hanzamzamy/arb-fpro/Dokumentasi/1.jpg

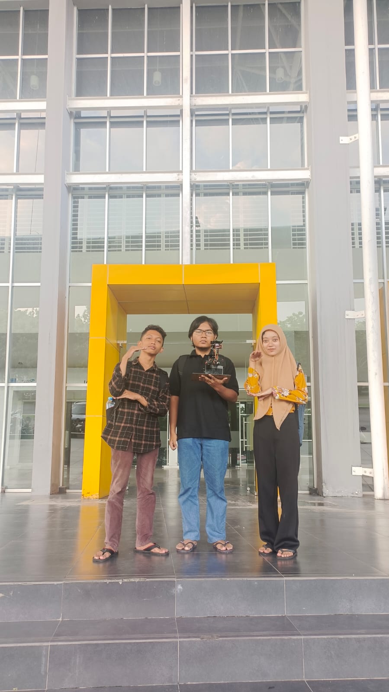
Dokumentasi/1.jpg
