hanzamzamy/arb-fpro/Dokumentasi/2.jpg

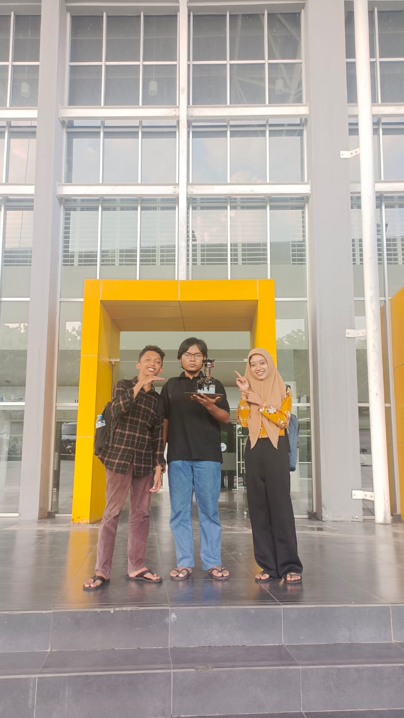
Dokumentasi/2.jpg
