hanzamzamy/arb-fpro/Dokumentasi/Barang e.jpg

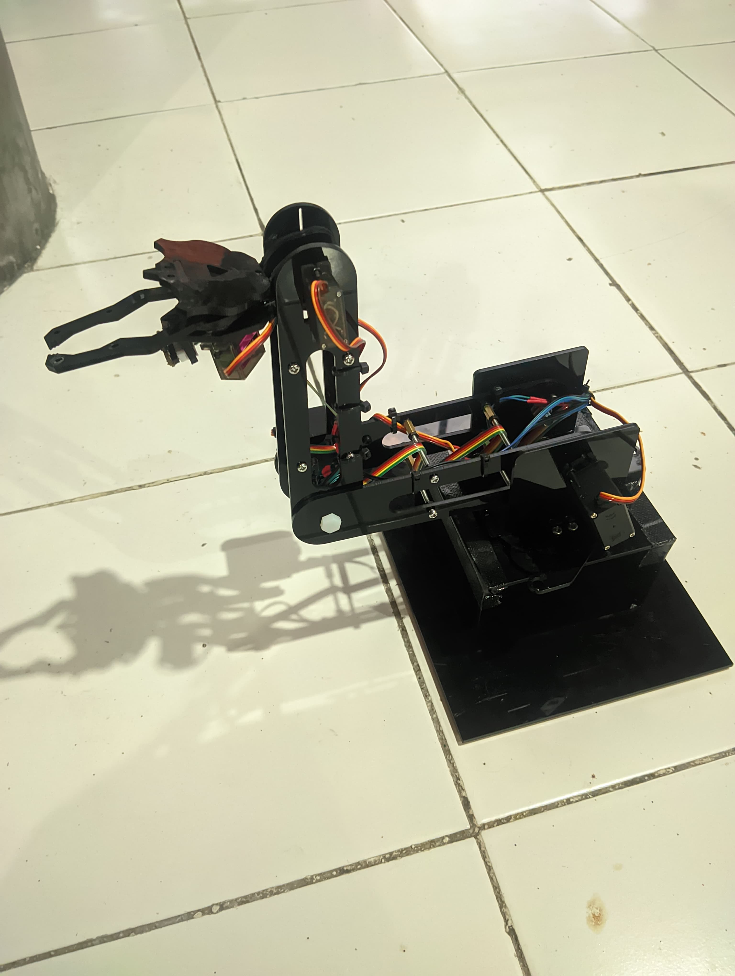
Dokumentasi/Barang e.jpg
