hanzamzamy/arb-fpro/Electrical/FP_Abinara/Controller_Render Bottom.png

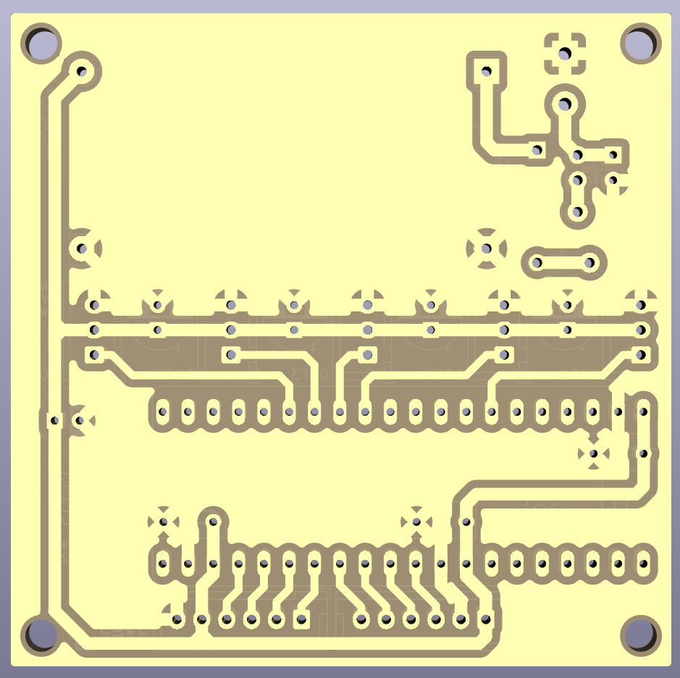
Electrical/FP_Abinara/Controller_Render Bottom.png
