hanzamzamy/arb-fpro/Electrical/FP_Abinara/Controller_Render Top.png

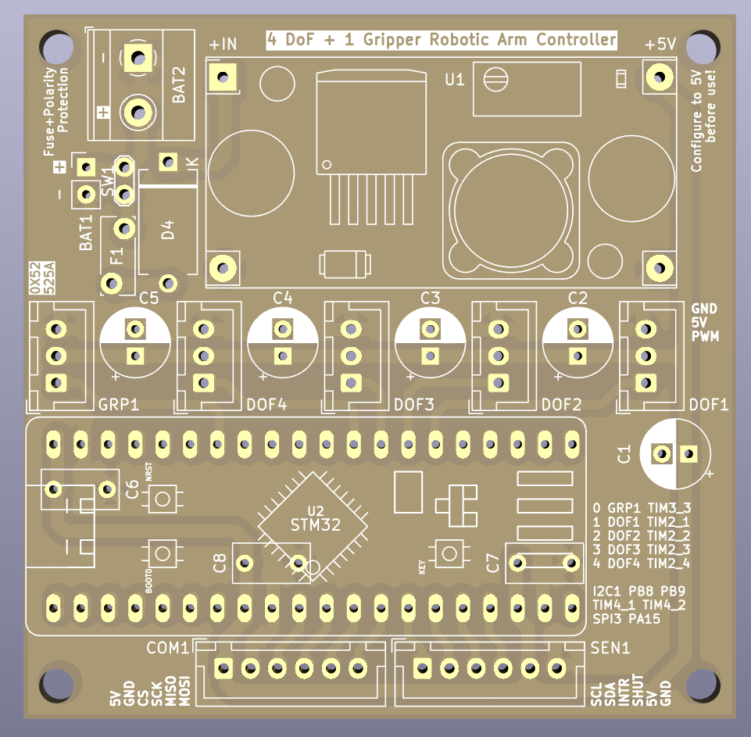
Electrical/FP_Abinara/Controller_Render Top.png
