hanzamzamy/arb-fpro/Mechanical/Macrobot_Silvia Nur Aziza_Mechanical/1b70d2714a9770270d7ed8d73e5aa972.jpg

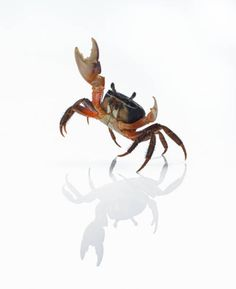
Mechanical/Macrobot_Silvia Nur Aziza_Mechanical/1b70d2714a9770270d7ed8d73e5aa972.jpg
