hanzamzamy/arb-fpro/Mechanical/Macrobot_Silvia Nur Aziza_Mechanical/1f14c011dfd35143ff6038cf6c039e9c.jpg

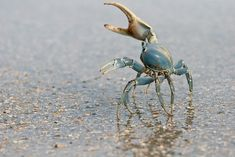
Mechanical/Macrobot_Silvia Nur Aziza_Mechanical/1f14c011dfd35143ff6038cf6c039e9c.jpg
