hanzamzamy/arb-fpro/Mechanical/Macrobot_Silvia Nur Aziza_Mechanical/5ebacc5fd523165728d35504ef82c865.jpg

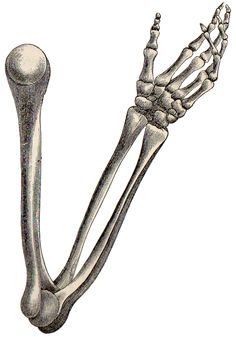
Mechanical/Macrobot_Silvia Nur Aziza_Mechanical/5ebacc5fd523165728d35504ef82c865.jpg
