hanzamzamy/arb-fpro/Mechanical/Macrobot_Silvia Nur Aziza_Mechanical/6f040f222747fe39410e0ac93c5bb1eb.jpg

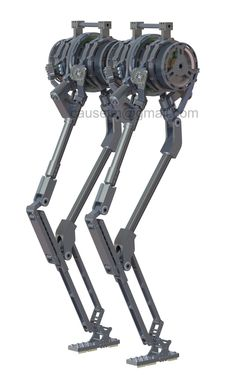
Mechanical/Macrobot_Silvia Nur Aziza_Mechanical/6f040f222747fe39410e0ac93c5bb1eb.jpg
