hanzamzamy/arb-fpro/Mechanical/Macrobot_Silvia Nur Aziza_Mechanical/7bddb617da2399516741761e50cced2f.jpg

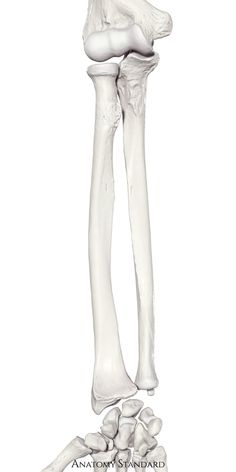
Mechanical/Macrobot_Silvia Nur Aziza_Mechanical/7bddb617da2399516741761e50cced2f.jpg
