hanzamzamy/arb-fpro/Mechanical/Macrobot_Silvia Nur Aziza_Mechanical/9b21c861dd7363406e4008cd5ddb0c76.jpg

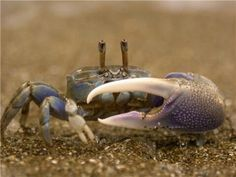
Mechanical/Macrobot_Silvia Nur Aziza_Mechanical/9b21c861dd7363406e4008cd5ddb0c76.jpg
