hanzamzamy/arb-fpro/Mechanical/Macrobot_Silvia Nur Aziza_Mechanical/22eb1ead862de790698cb6ff54a92b3c.jpg

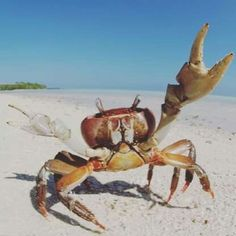
Mechanical/Macrobot_Silvia Nur Aziza_Mechanical/22eb1ead862de790698cb6ff54a92b3c.jpg
