hanzamzamy/arb-fpro/Mechanical/Macrobot_Silvia Nur Aziza_Mechanical/24a283ecc0165925ef94e39cae853259.jpg

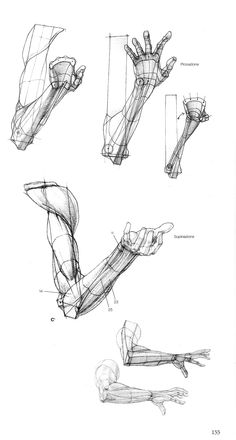
Mechanical/Macrobot_Silvia Nur Aziza_Mechanical/24a283ecc0165925ef94e39cae853259.jpg
