hanzamzamy/arb-fpro/Mechanical/Macrobot_Silvia Nur Aziza_Mechanical/52b4f24d89aa3ba14f1d6c219212160f.jpg

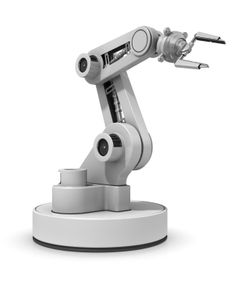
Mechanical/Macrobot_Silvia Nur Aziza_Mechanical/52b4f24d89aa3ba14f1d6c219212160f.jpg
