hanzamzamy/arb-fpro/Mechanical/Macrobot_Silvia Nur Aziza_Mechanical/71ebfb8fe3e344c98b983a9f49a2de56.jpg

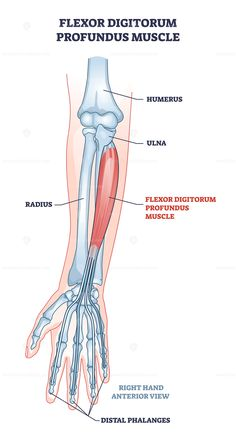
Mechanical/Macrobot_Silvia Nur Aziza_Mechanical/71ebfb8fe3e344c98b983a9f49a2de56.jpg
