hanzamzamy/arb-fpro/Mechanical/Macrobot_Silvia Nur Aziza_Mechanical/74ea5ec94e9108678c05d65d293ccad4.jpg

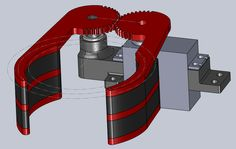
Mechanical/Macrobot_Silvia Nur Aziza_Mechanical/74ea5ec94e9108678c05d65d293ccad4.jpg
