hanzamzamy/arb-fpro/Mechanical/Macrobot_Silvia Nur Aziza_Mechanical/83fee2618bc4fb25e195a0beeff81b47.jpg

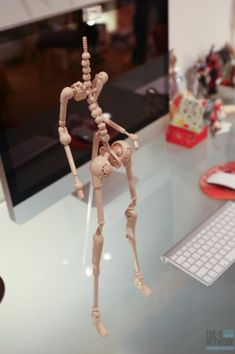
Mechanical/Macrobot_Silvia Nur Aziza_Mechanical/83fee2618bc4fb25e195a0beeff81b47.jpg
