hanzamzamy/arb-fpro/Mechanical/Macrobot_Silvia Nur Aziza_Mechanical/400e2da95c83461e85157f70f1b9e926.jpg

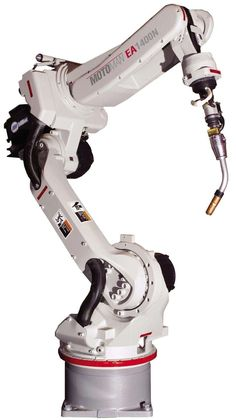
Mechanical/Macrobot_Silvia Nur Aziza_Mechanical/400e2da95c83461e85157f70f1b9e926.jpg
