hanzamzamy/arb-fpro/Mechanical/Macrobot_Silvia Nur Aziza_Mechanical/895d9e59c8b177fc4fbb9f1e9df40633.jpg

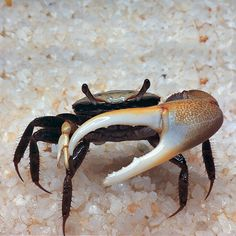
Mechanical/Macrobot_Silvia Nur Aziza_Mechanical/895d9e59c8b177fc4fbb9f1e9df40633.jpg
