hanzamzamy/arb-fpro/Mechanical/Macrobot_Silvia Nur Aziza_Mechanical/4187bd70cf4623def9ee9aae4583c98c.jpg

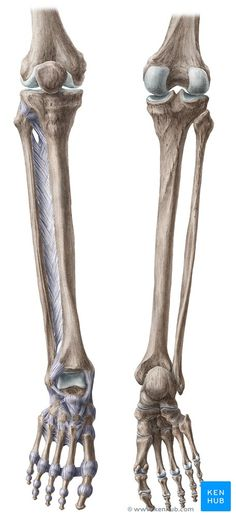
Mechanical/Macrobot_Silvia Nur Aziza_Mechanical/4187bd70cf4623def9ee9aae4583c98c.jpg
