hanzamzamy/arb-fpro/Mechanical/Macrobot_Silvia Nur Aziza_Mechanical/19350de375ecb00b500f2bd80deb1692.jpg

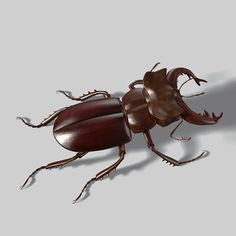
Mechanical/Macrobot_Silvia Nur Aziza_Mechanical/19350de375ecb00b500f2bd80deb1692.jpg
