hanzamzamy/arb-fpro/Mechanical/Macrobot_Silvia Nur Aziza_Mechanical/71604eb40ae7a4ac1df7c45119ac012c.jpg

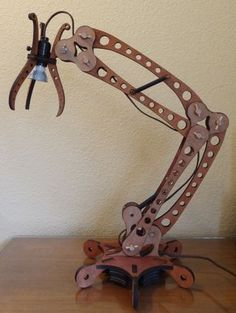
Mechanical/Macrobot_Silvia Nur Aziza_Mechanical/71604eb40ae7a4ac1df7c45119ac012c.jpg
