hanzamzamy/arb-fpro/Mechanical/Macrobot_Silvia Nur Aziza_Mechanical/97079ea19a3d9b3a081851db0ce27ebf.jpg

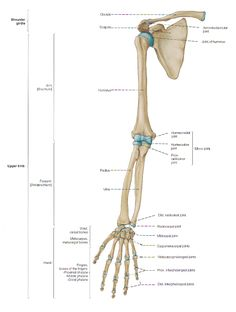
Mechanical/Macrobot_Silvia Nur Aziza_Mechanical/97079ea19a3d9b3a081851db0ce27ebf.jpg
