hanzamzamy/arb-fpro/Mechanical/Macrobot_Silvia Nur Aziza_Mechanical/848779f3e6584e807d604cdb2f7c47b8.jpg

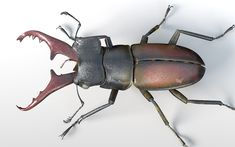
Mechanical/Macrobot_Silvia Nur Aziza_Mechanical/848779f3e6584e807d604cdb2f7c47b8.jpg
