hanzamzamy/arb-fpro/Mechanical/Macrobot_Silvia Nur Aziza_Mechanical/c9f90fcedc622ee27020b8a11ae0bc79.jpg

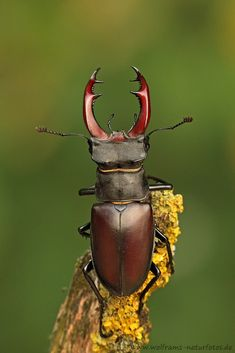
Mechanical/Macrobot_Silvia Nur Aziza_Mechanical/c9f90fcedc622ee27020b8a11ae0bc79.jpg
