hanzamzamy/arb-fpro/Mechanical/Macrobot_Silvia Nur Aziza_Mechanical/c50b781b7837ca079c64433cbba6b4cd.jpg

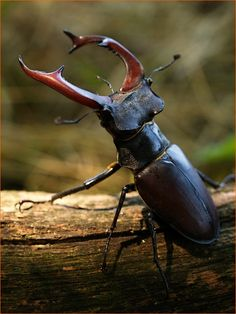
Mechanical/Macrobot_Silvia Nur Aziza_Mechanical/c50b781b7837ca079c64433cbba6b4cd.jpg
