hanzamzamy/arb-fpro/Mechanical/Macrobot_Silvia Nur Aziza_Mechanical/cb312d82ace88d422fab98ad79ffac79.jpg

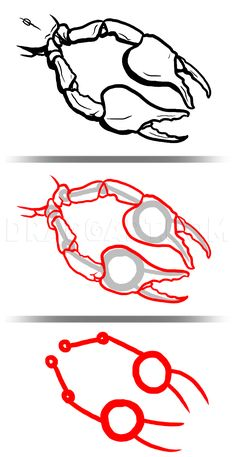
Mechanical/Macrobot_Silvia Nur Aziza_Mechanical/cb312d82ace88d422fab98ad79ffac79.jpg
