hanzamzamy/arb-fpro/Mechanical/Macrobot_Silvia Nur Aziza_Mechanical/debb197d7bb12a75175ac4dd222c4765.jpg

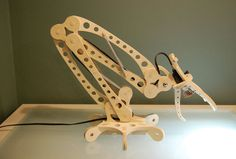
Mechanical/Macrobot_Silvia Nur Aziza_Mechanical/debb197d7bb12a75175ac4dd222c4765.jpg
