hanzamzamy/arb-fpro/Mechanical/Macrobot_Silvia Nur Aziza_Mechanical/e524af7c66d48fa53c7d827c05bd7dcf.jpg

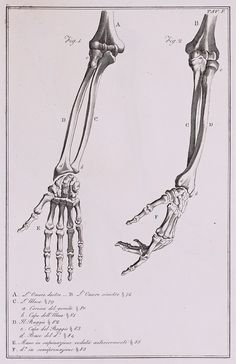
Mechanical/Macrobot_Silvia Nur Aziza_Mechanical/e524af7c66d48fa53c7d827c05bd7dcf.jpg
