hanzamzamy/arb-fpro/Mechanical/Macrobot_Silvia Nur Aziza_Mechanical/WhatsApp Image 2024-02-11 at 00.09.53 (1).jpeg

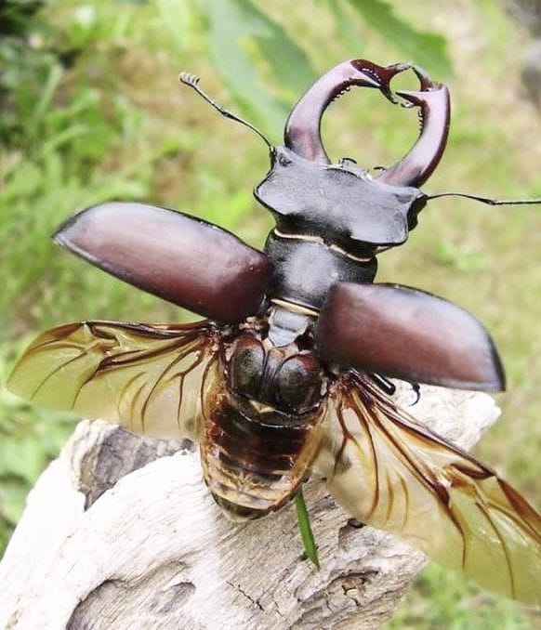
Mechanical/Macrobot_Silvia Nur Aziza_Mechanical/WhatsApp Image 2024-02-11 at 00.09.53 (1).jpeg
