hanzamzamy/arb-fpro/Mechanical/Macrobot_Silvia Nur Aziza_Mechanical/WhatsApp Image 2024-02-11 at 09.15.11 (1).jpeg

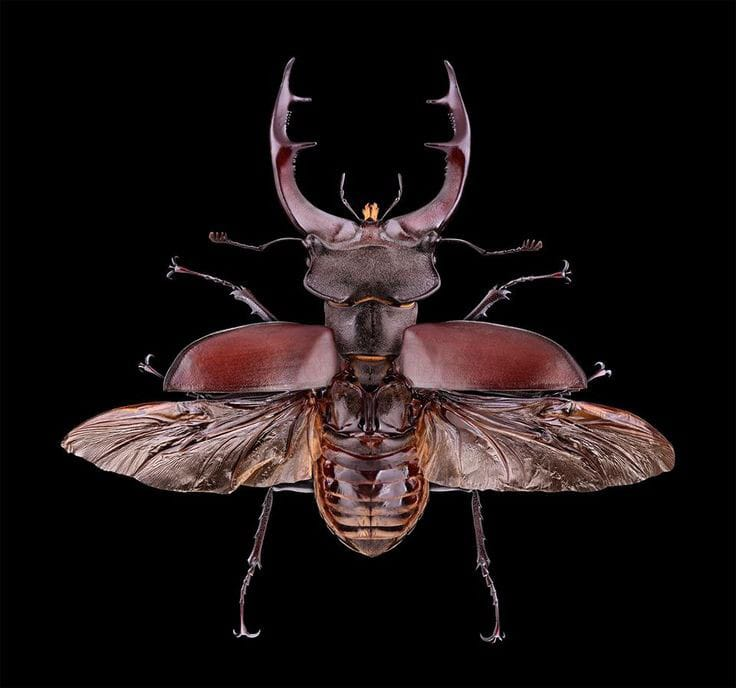
Mechanical/Macrobot_Silvia Nur Aziza_Mechanical/WhatsApp Image 2024-02-11 at 09.15.11 (1).jpeg
