hanzamzamy/arb-fpro/Programming/easeinout.png

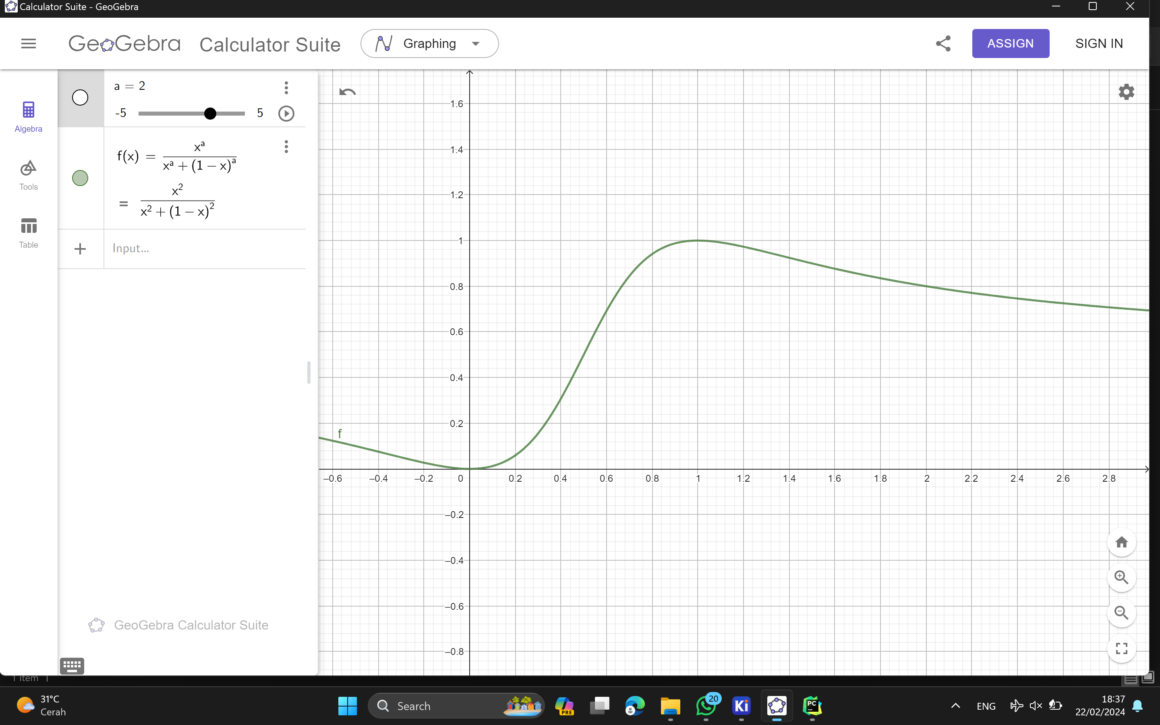
Programming/easeinout.png
