hanzamzamy/arb-fpro/Programming/urdfmodel.png

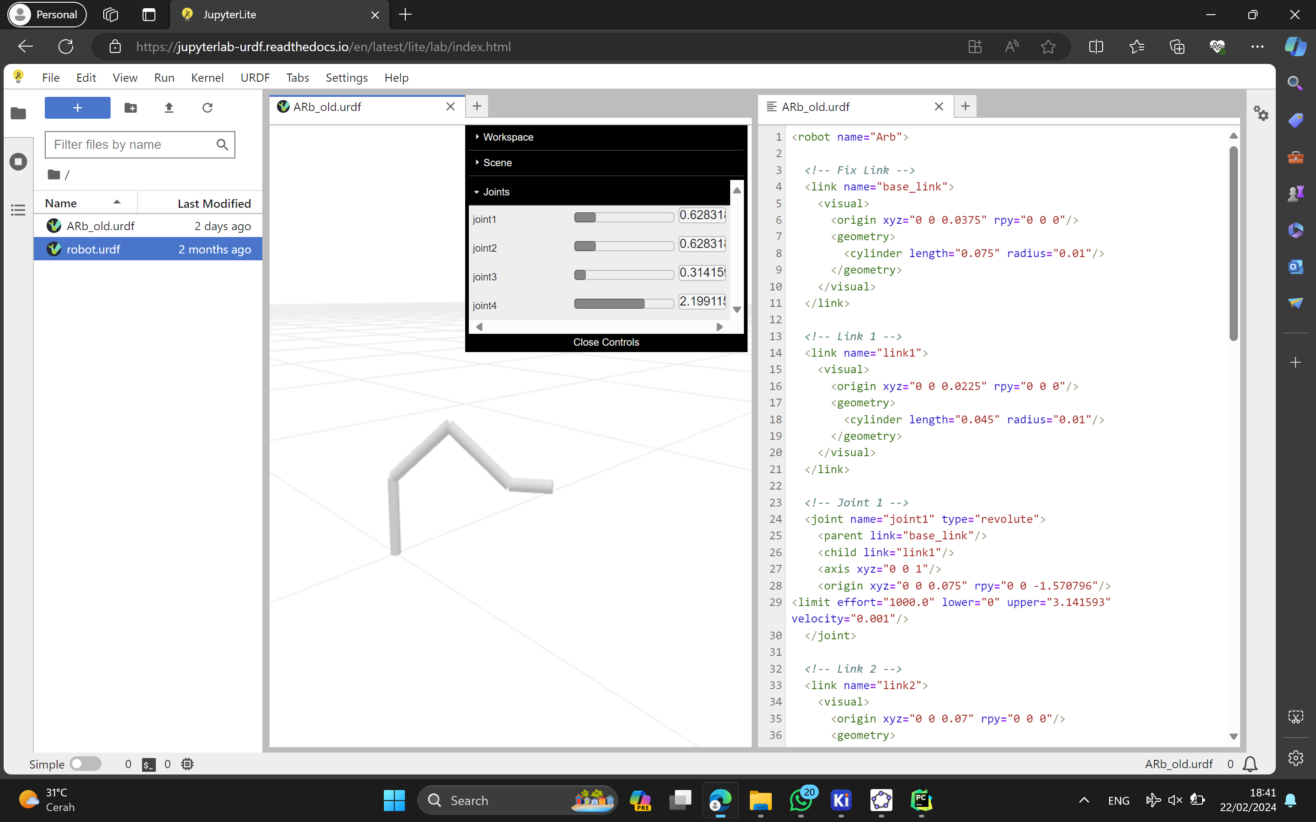
Programming/urdfmodel.png
