hanzamzamy/arb-fpro/Mechanical/Macrobot_Silvia Nur Aziza_Mechanical/mg996-servo-motor-180-1.snapshot.1/Servo MG995 180/Servo MG995.SLDPRT

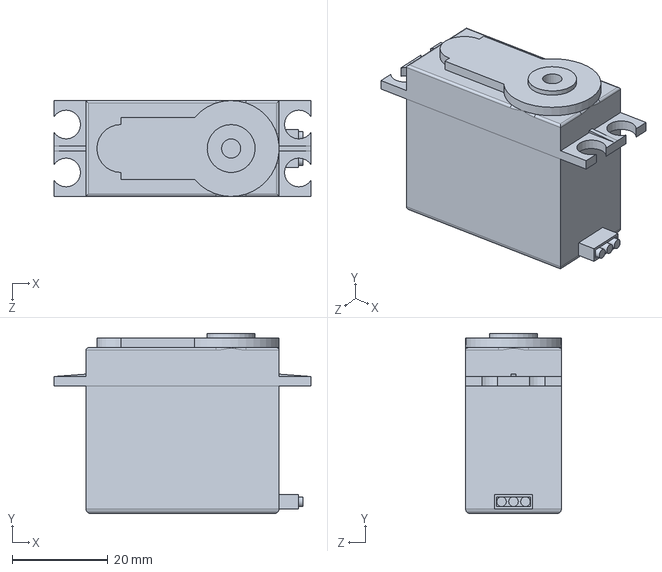
[picture p57: CAD file, 2024-02-22]
Mechanical/Macrobot_Silvia Nur Aziza_Mechanical/mg996-servo-motor-180-1.snapshot.1/Servo MG995 180/Servo MG995.SLDPRT
53.6 x 37.6 x 20.0 mm
