hanzamzamy/arb-fpro/Mechanical/Macrobot_Silvia Nur Aziza_Mechanical/refisni/db 2 - Copy.SLDPRT

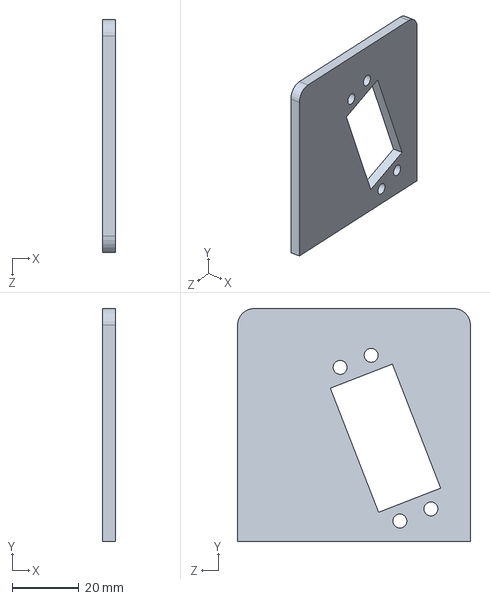
[picture p58: CAD file, 2024-02-22]
Mechanical/Macrobot_Silvia Nur Aziza_Mechanical/refisni/db 2 - Copy.SLDPRT
4.00 x 70.0 x 70.0 mm
