hanzamzamy/arb-fpro/Mechanical/Macrobot_Silvia Nur Aziza_Mechanical/kiri untuk perhitungan sketsa.SLDPRT

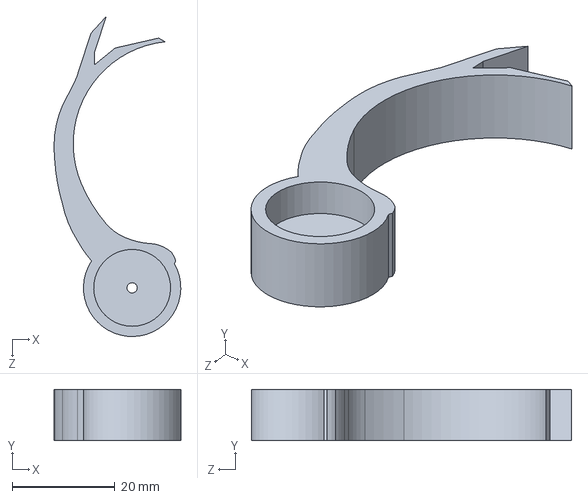
[picture p59: CAD file, 2024-02-22]
Mechanical/Macrobot_Silvia Nur Aziza_Mechanical/kiri untuk perhitungan sketsa.SLDPRT
24.7 x 10.0 x 62.4 mm
