hanzamzamy/arb-fpro/Mechanical/Macrobot_Silvia Nur Aziza_Mechanical/FP23_Object.SLDPRT

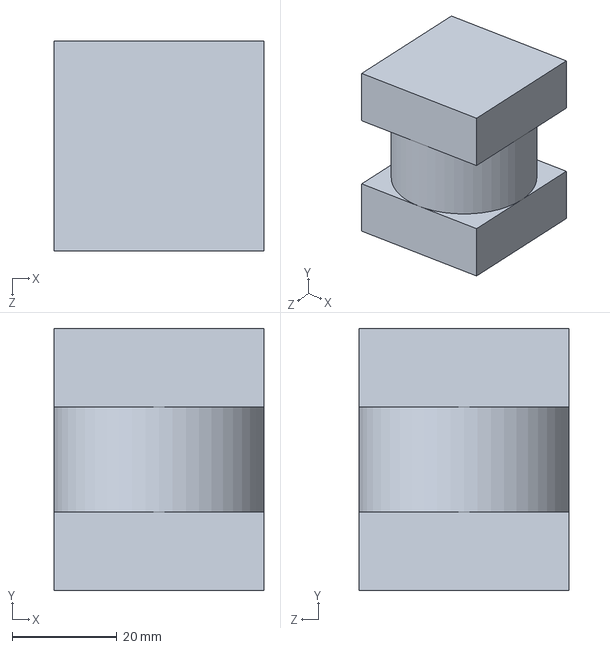
[picture p60: CAD file, 2024-02-22]
Mechanical/Macrobot_Silvia Nur Aziza_Mechanical/FP23_Object.SLDPRT
40.0 x 50.0 x 40.0 mm
