hanzamzamy/arb-fpro/Mechanical/Macrobot_Silvia Nur Aziza_Mechanical/refisni/revisi base.SLDPRT

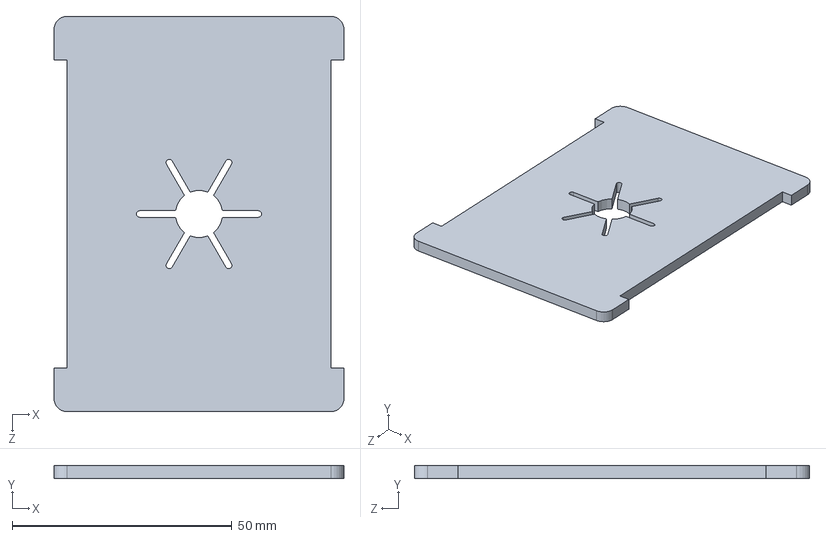
[picture p61: CAD file, 2024-02-22]
Mechanical/Macrobot_Silvia Nur Aziza_Mechanical/refisni/revisi base.SLDPRT
66.0 x 3.00 x 90.0 mm
