hanzamzamy/arb-fpro/Mechanical/Macrobot_Silvia Nur Aziza_Mechanical/refisni/bawah - Copy.SLDPRT

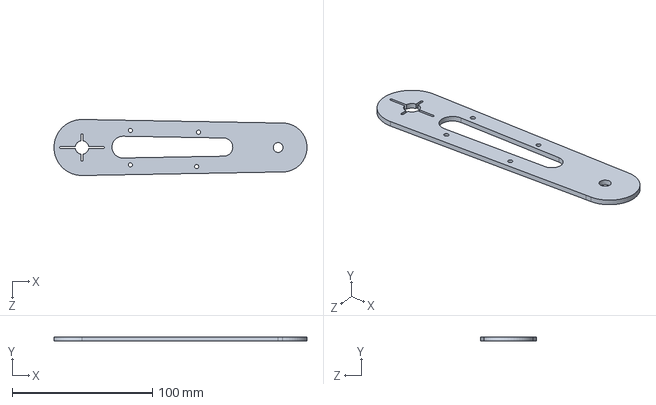
[picture p62: CAD file, 2024-02-22]
Mechanical/Macrobot_Silvia Nur Aziza_Mechanical/refisni/bawah - Copy.SLDPRT
180.6 x 3.00 x 40.0 mm
