hanzamzamy/arb-fpro/Mechanical/Macrobot_Silvia Nur Aziza_Mechanical/monting.SLDPRT

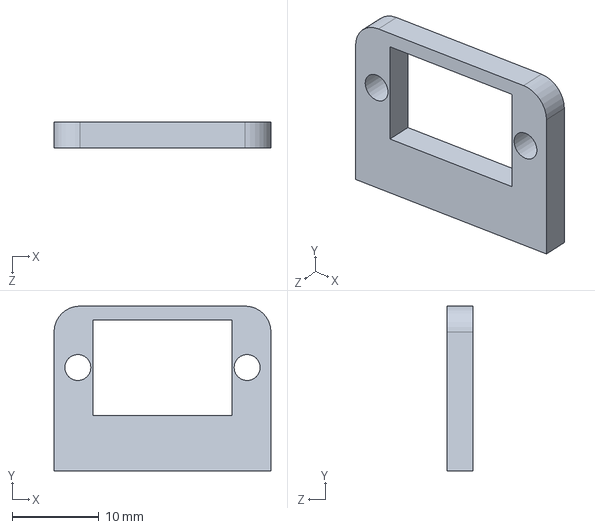
[picture p63: CAD file, 2024-02-22]
Mechanical/Macrobot_Silvia Nur Aziza_Mechanical/monting.SLDPRT
25.0 x 19.0 x 3.00 mm
