hanzamzamy/arb-fpro/Mechanical/Macrobot_Silvia Nur Aziza_Mechanical/0atas kiri pjg.SLDPRT

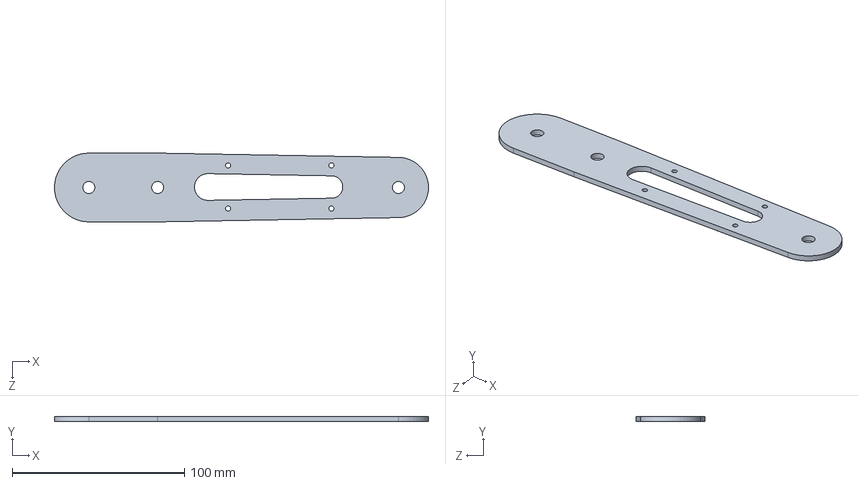
[picture p64: CAD file, 2024-02-22]
Mechanical/Macrobot_Silvia Nur Aziza_Mechanical/0atas kiri pjg.SLDPRT
217.4 x 3.00 x 40.0 mm
