hanzamzamy/arb-fpro/Mechanical/Macrobot_Silvia Nur Aziza_Mechanical/kanan fiks.SLDPRT

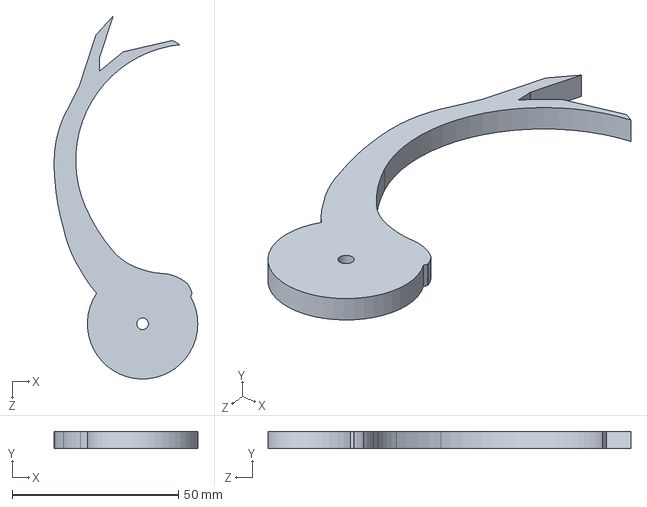
[picture p65: CAD file, 2024-02-22]
Mechanical/Macrobot_Silvia Nur Aziza_Mechanical/kanan fiks.SLDPRT
43.2 x 5.25 x 109.3 mm
