hanzamzamy/arb-fpro/Mechanical/Macrobot_Silvia Nur Aziza_Mechanical/tatakan griper bawah - Copy.SLDPRT

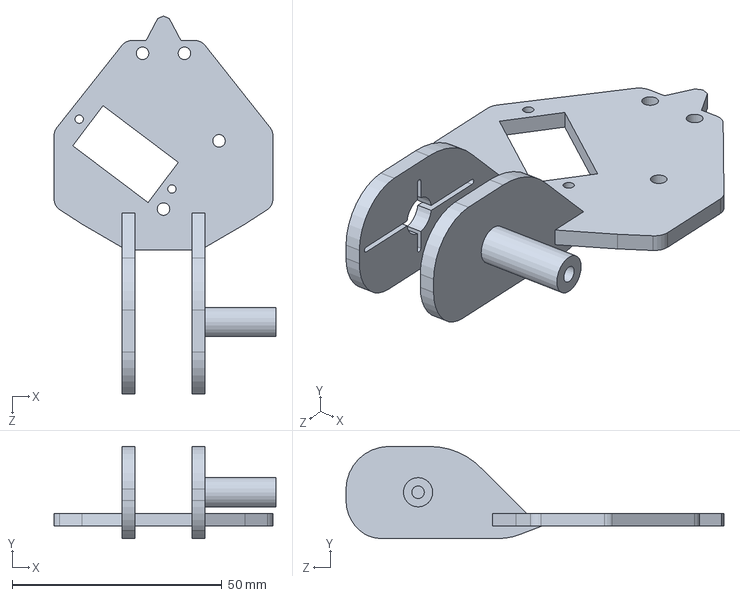
[picture p66: CAD file, 2024-02-22]
Mechanical/Macrobot_Silvia Nur Aziza_Mechanical/tatakan griper bawah - Copy.SLDPRT
53.0 x 22.0 x 90.2 mm
