hanzamzamy/arb-fpro/Mechanical/Macrobot_Silvia Nur Aziza_Mechanical/bassseeesss.SLDPRT

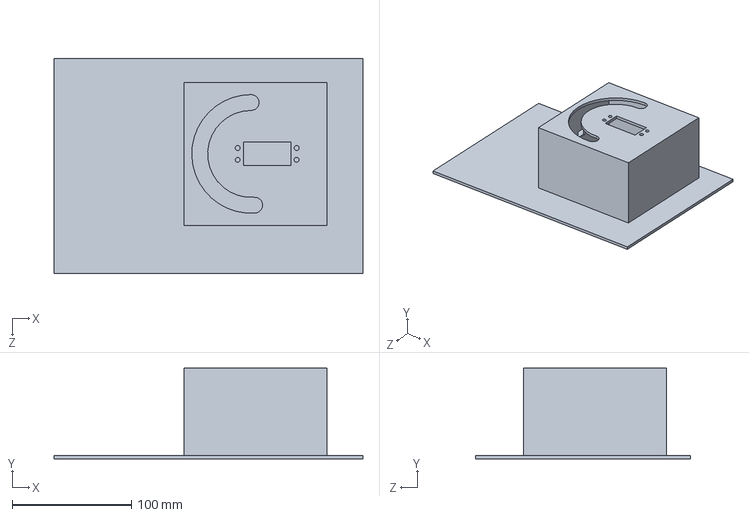
[picture p67: CAD file, 2024-02-22]
Mechanical/Macrobot_Silvia Nur Aziza_Mechanical/bassseeesss.SLDPRT
259.0 x 76.0 x 180.3 mm
