hanzamzamy/arb-fpro/Mechanical/Macrobot_Silvia Nur Aziza_Mechanical/kiri baguss.SLDPRT

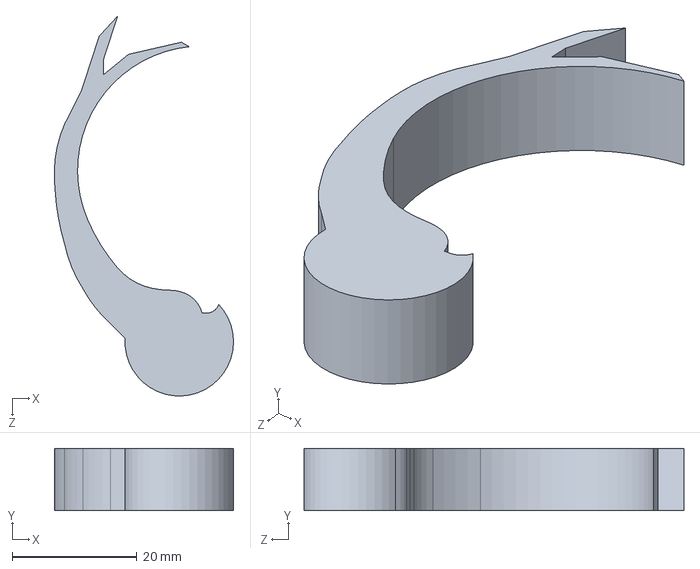
[picture p68: CAD file, 2024-02-22]
Mechanical/Macrobot_Silvia Nur Aziza_Mechanical/kiri baguss.SLDPRT
28.8 x 10.0 x 61.0 mm
