hanzamzamy/arb-fpro/Mechanical/Macrobot_Silvia Nur Aziza_Mechanical/griper kanan fiks.SLDPRT

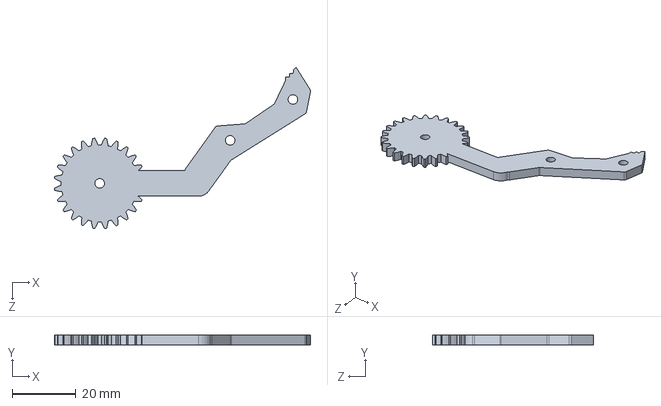
[picture p69: CAD file, 2024-02-22]
Mechanical/Macrobot_Silvia Nur Aziza_Mechanical/griper kanan fiks.SLDPRT
80.2 x 3.00 x 50.5 mm
