hanzamzamy/arb-fpro/Mechanical/Macrobot_Silvia Nur Aziza_Mechanical/tb 2.SLDPRT

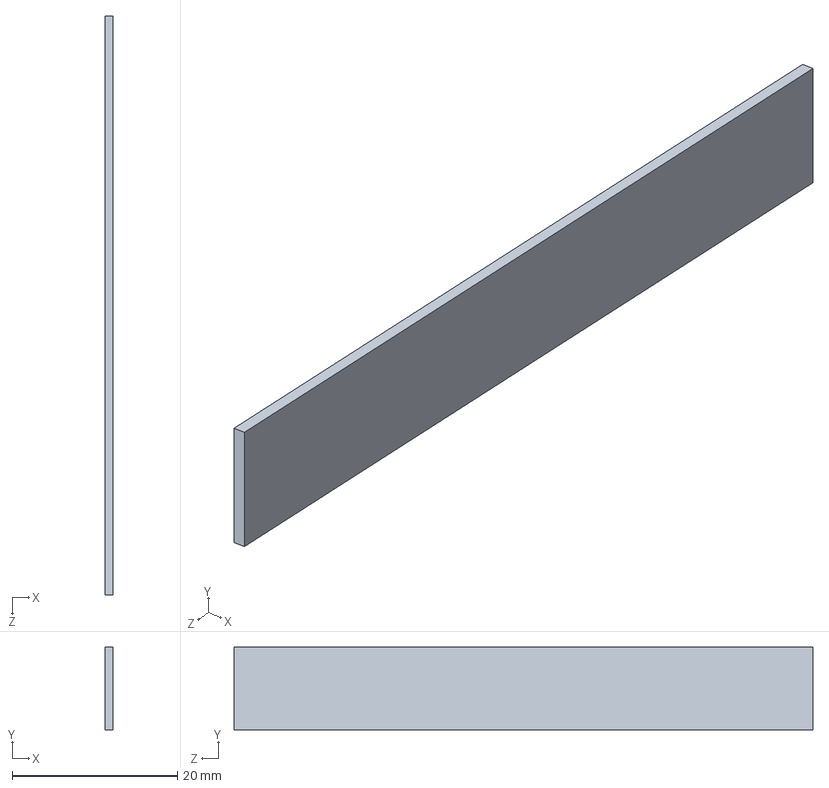
[picture p70: CAD file, 2024-02-22]
Mechanical/Macrobot_Silvia Nur Aziza_Mechanical/tb 2.SLDPRT
1.00 x 10.0 x 70.0 mm
