hanzamzamy/arb-fpro/Mechanical/Macrobot_Silvia Nur Aziza_Mechanical/penggerak.SLDPRT

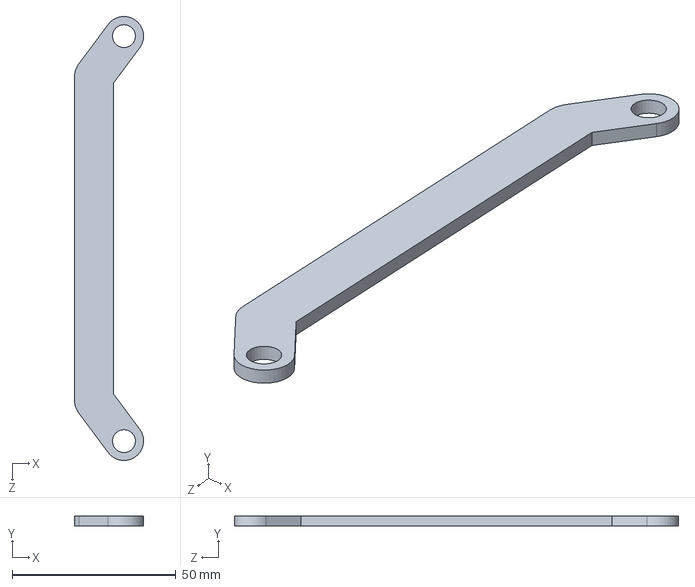
[picture p72: CAD file, 2024-02-22]
Mechanical/Macrobot_Silvia Nur Aziza_Mechanical/penggerak.SLDPRT
21.1 x 3.00 x 135.6 mm
