hanzamzamy/arb-fpro/Mechanical/Macrobot_Silvia Nur Aziza_Mechanical/Robot base.SLDPRT

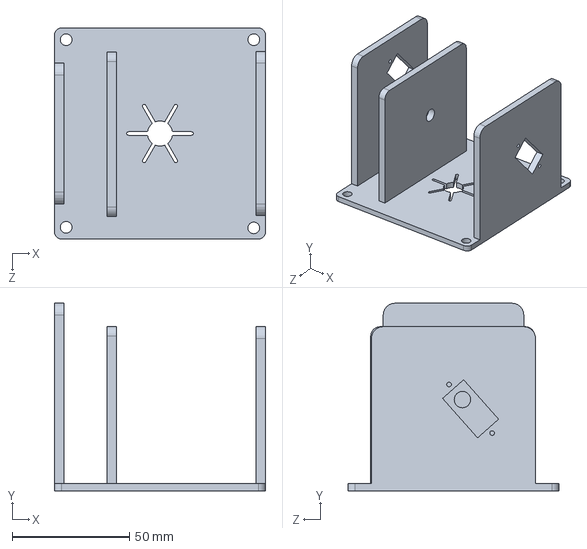
[picture p73: CAD file, 2024-02-22]
Mechanical/Macrobot_Silvia Nur Aziza_Mechanical/Robot base.SLDPRT
90.0 x 80.0 x 90.0 mm
