hanzamzamy/arb-fpro/Mechanical/Macrobot_Silvia Nur Aziza_Mechanical/Silvia Nur Aziza_cetak akrilik.DXF

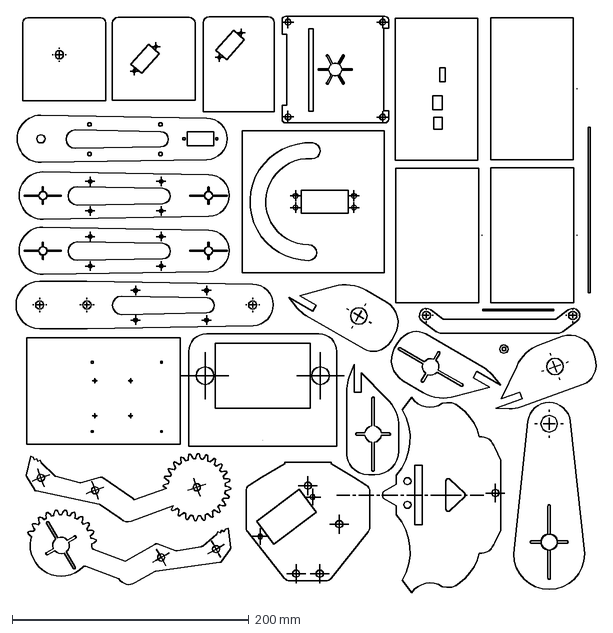
[picture p74: CAD file, 2024-02-22]
Mechanical/Macrobot_Silvia Nur Aziza_Mechanical/Silvia Nur Aziza_cetak akrilik.DXF
491.0 x 487.1 mm
