hanzamzamy/arb-fpro/Mechanical/Macrobot_Silvia Nur Aziza_Mechanical/Gripper - Copy.SLDPRT

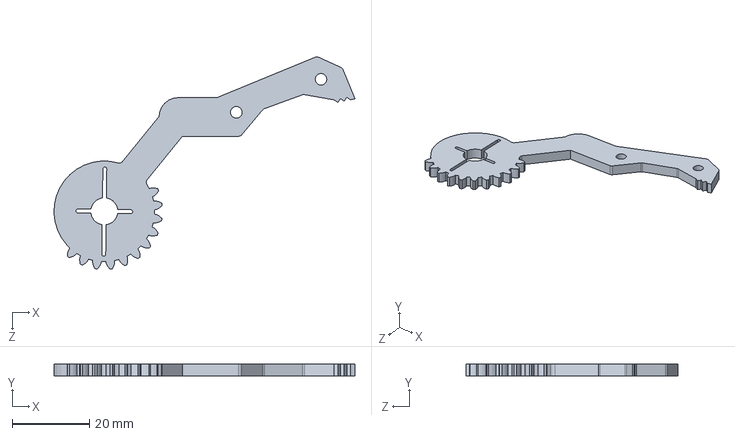
[picture p75: CAD file, 2024-02-22]
Mechanical/Macrobot_Silvia Nur Aziza_Mechanical/Gripper - Copy.SLDPRT
77.7 x 3.00 x 54.8 mm
