hanzamzamy/arb-fpro/Mechanical/Macrobot_Silvia Nur Aziza_Mechanical/bs2.SLDPRT

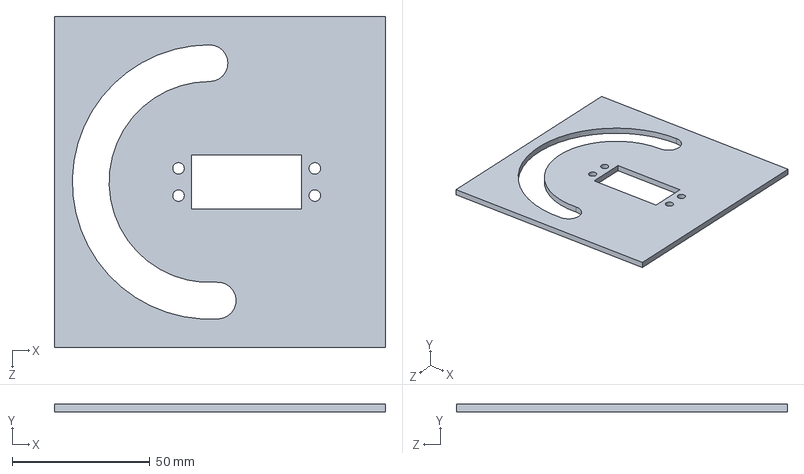
[picture p76: CAD file, 2024-02-22]
Mechanical/Macrobot_Silvia Nur Aziza_Mechanical/bs2.SLDPRT
120.0 x 3.00 x 120.0 mm
