hanzamzamy/arb-fpro/Mechanical/Macrobot_Silvia Nur Aziza_Mechanical/tb 1.SLDPRT

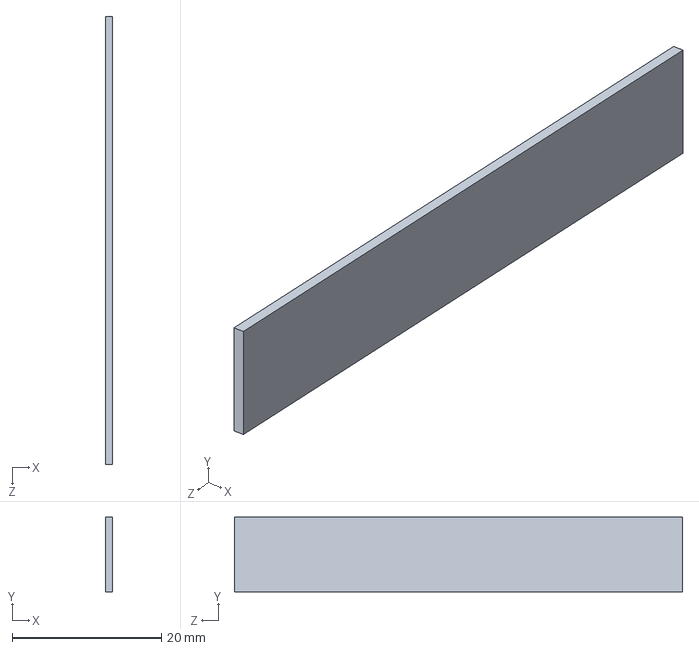
[picture p77: CAD file, 2024-02-22]
Mechanical/Macrobot_Silvia Nur Aziza_Mechanical/tb 1.SLDPRT
1.00 x 10.0 x 60.0 mm
