hanzamzamy/arb-fpro/Mechanical/Macrobot_Silvia Nur Aziza_Mechanical/db 1 .SLDPRT

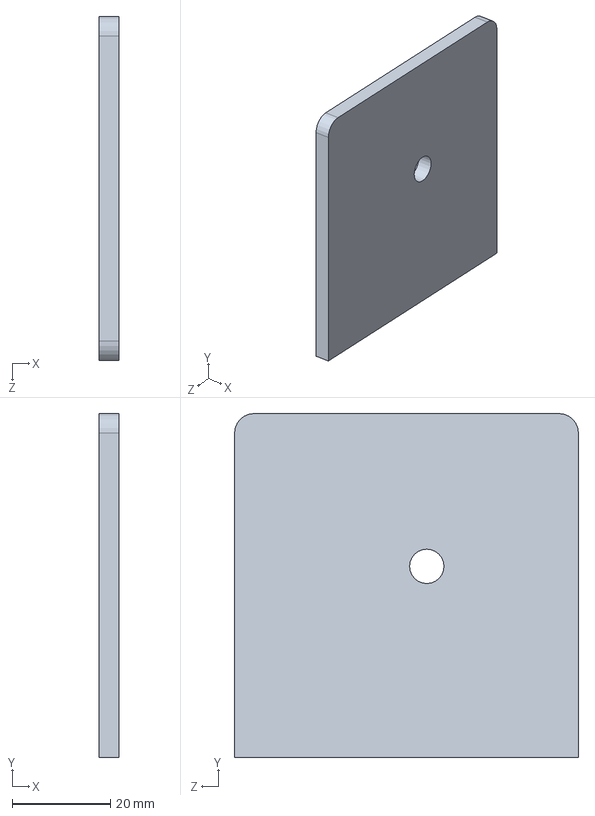
[picture p79: CAD file, 2024-02-22]
Mechanical/Macrobot_Silvia Nur Aziza_Mechanical/db 1 .SLDPRT
4.00 x 70.0 x 70.0 mm
