hanzamzamy/arb-fpro/Mechanical/Macrobot_Silvia Nur Aziza_Mechanical/spg 1.SLDPRT

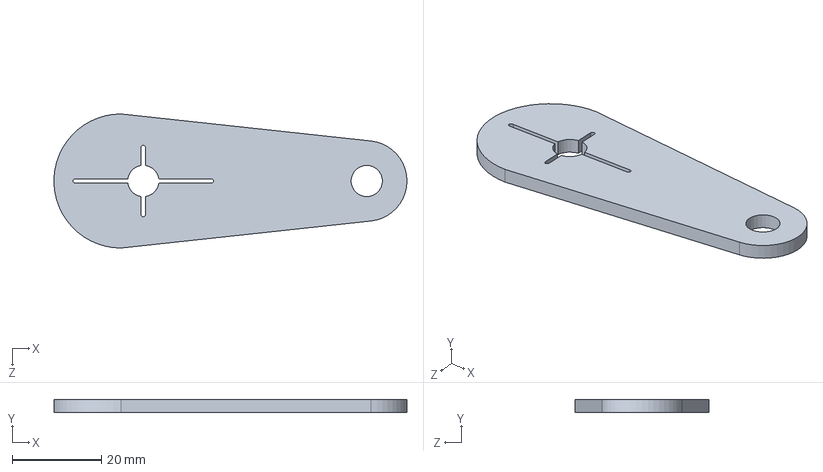
[picture p80: CAD file, 2024-02-22]
Mechanical/Macrobot_Silvia Nur Aziza_Mechanical/spg 1.SLDPRT
79.0 x 3.00 x 30.0 mm
