hanzamzamy/arb-fpro/Mechanical/Macrobot_Silvia Nur Aziza_Mechanical/baterai.SLDPRT

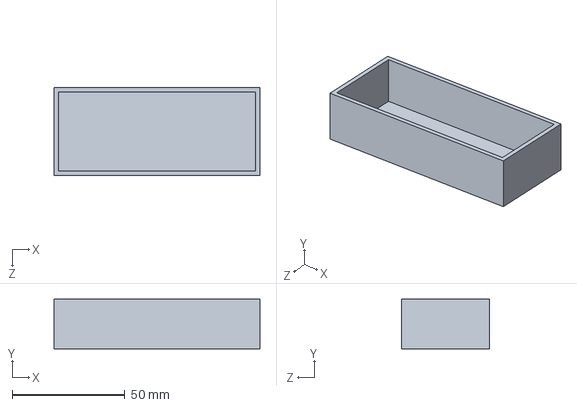
[picture p81: CAD file, 2024-02-22]
Mechanical/Macrobot_Silvia Nur Aziza_Mechanical/baterai.SLDPRT
91.5 x 22.0 x 39.0 mm
