hanzamzamy/arb-fpro/Mechanical/Macrobot_Silvia Nur Aziza_Mechanical/vl53l0x.STEP

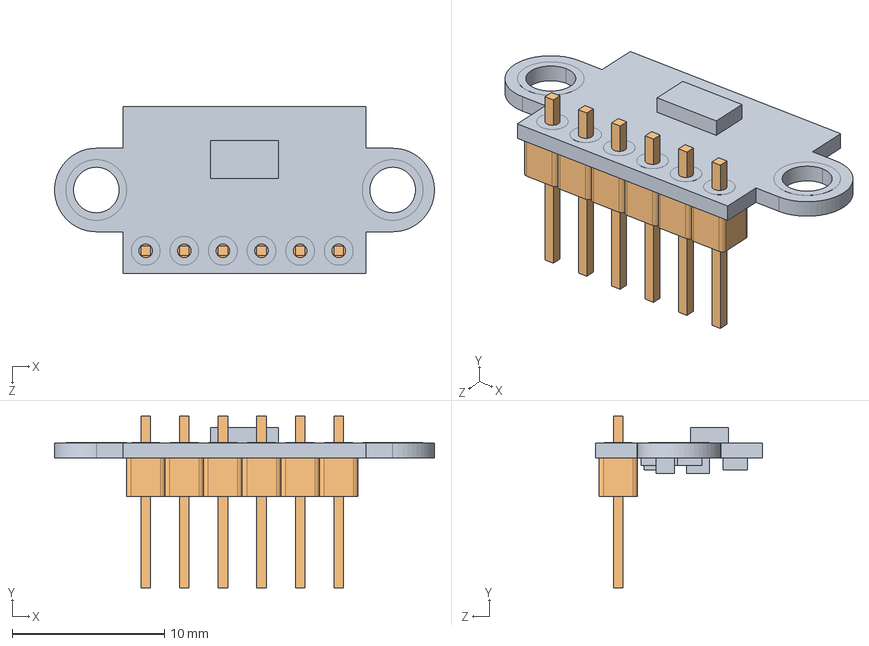
[picture p82: CAD file, 2024-02-22]
Mechanical/Macrobot_Silvia Nur Aziza_Mechanical/vl53l0x.STEP
25.0 x 11.3 x 11.0 mm
vl53l0x_PCB
pin_header x 6
