hanzamzamy/arb-fpro/Mechanical/Macrobot_Silvia Nur Aziza_Mechanical/bs 3.SLDPRT

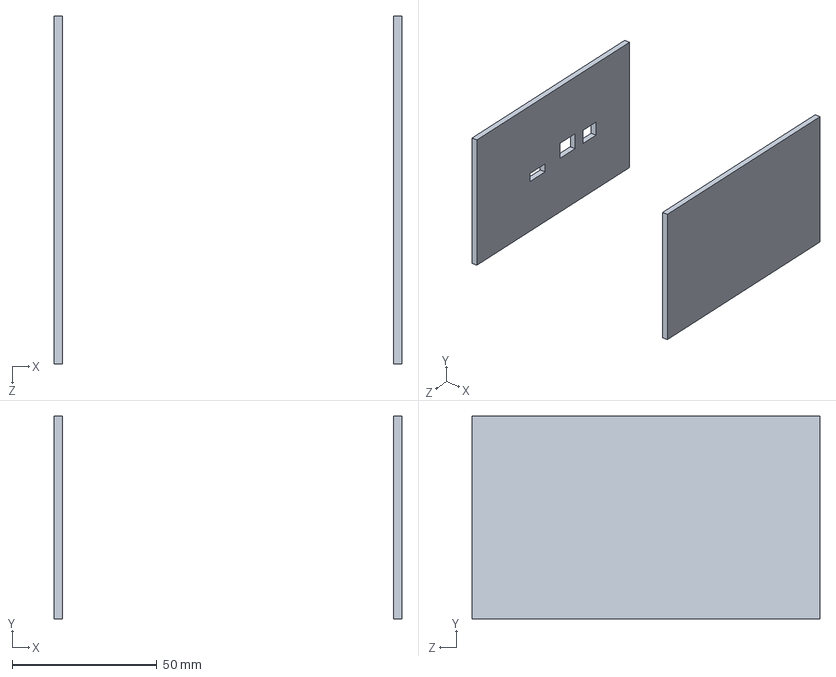
[picture p83: CAD file, 2024-02-22]
Mechanical/Macrobot_Silvia Nur Aziza_Mechanical/bs 3.SLDPRT
120.0 x 70.0 x 120.0 mm
