hanzamzamy/arb-fpro/Mechanical/Macrobot_Silvia Nur Aziza_Mechanical/kepala bolong.SLDPRT

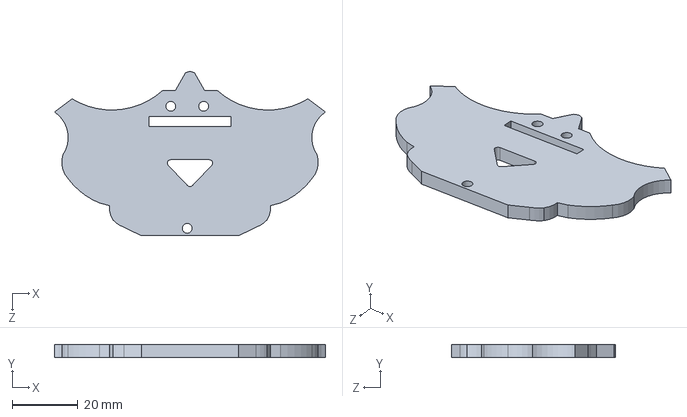
[picture p84: CAD file, 2024-02-22]
Mechanical/Macrobot_Silvia Nur Aziza_Mechanical/kepala bolong.SLDPRT
82.6 x 4.00 x 50.1 mm
