hanzamzamy/arb-fpro/Mechanical/Macrobot_Silvia Nur Aziza_Mechanical/0 bs 1.SLDPRT

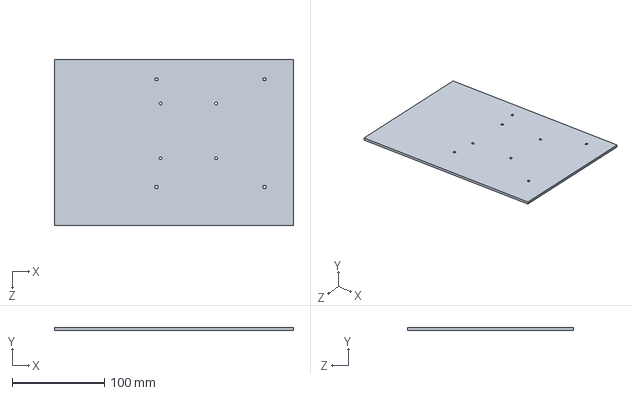
[picture p85: CAD file, 2024-02-22]
Mechanical/Macrobot_Silvia Nur Aziza_Mechanical/0 bs 1.SLDPRT
259.0 x 3.00 x 180.3 mm
