hanzamzamy/arb-fpro/Mechanical/Macrobot_Silvia Nur Aziza_Mechanical/tb 3 lgkrn.SLDPRT

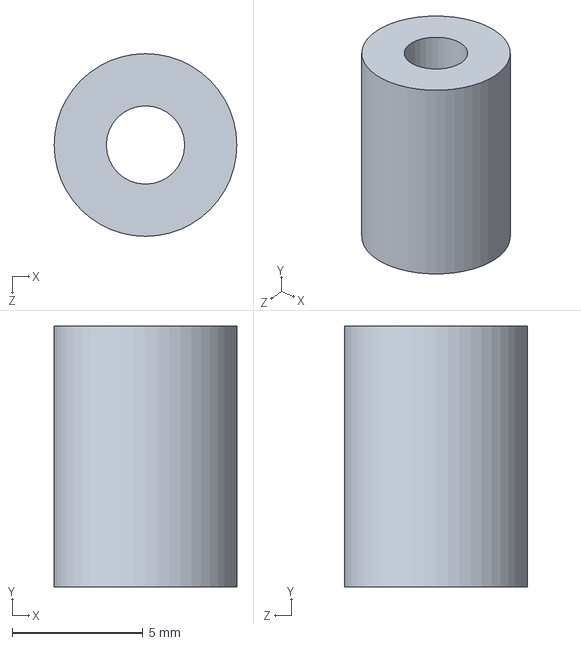
[picture p86: CAD file, 2024-02-22]
Mechanical/Macrobot_Silvia Nur Aziza_Mechanical/tb 3 lgkrn.SLDPRT
7.00 x 10.0 x 7.00 mm
