hanzamzamy/arb-fpro/Mechanical/Macrobot_Silvia Nur Aziza_Mechanical/UTS.MINI ROCKER SWITCH SENA Part.SLDPRT

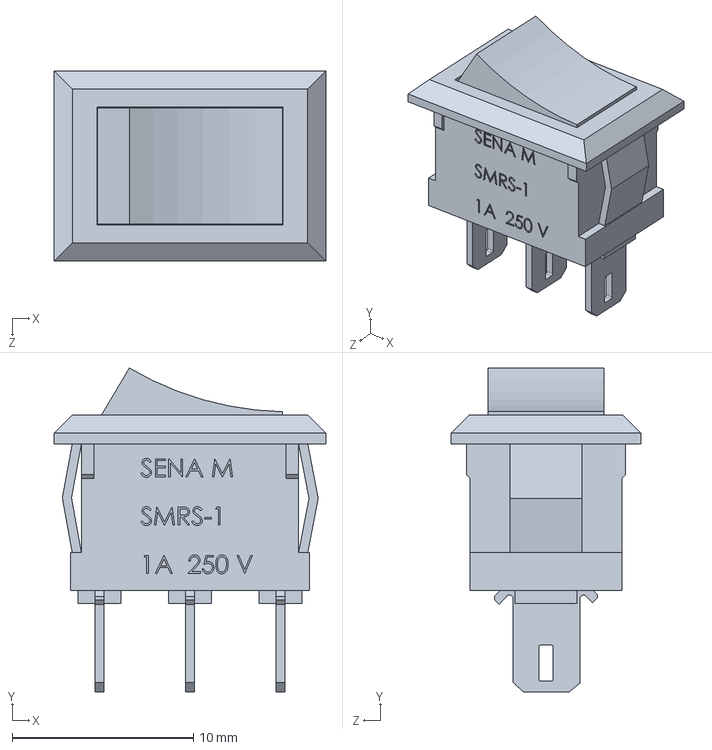
[picture p87: CAD file, 2024-02-22]
Mechanical/Macrobot_Silvia Nur Aziza_Mechanical/UTS.MINI ROCKER SWITCH SENA Part.SLDPRT
15.0 x 17.9 x 10.5 mm
