hanzamzamy/arb-fpro/Mechanical/Macrobot_Silvia Nur Aziza_Mechanical/db3.SLDPRT

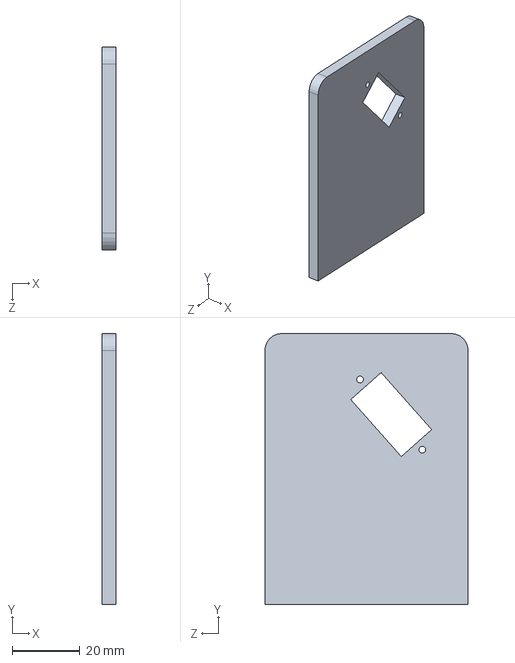
[picture p88: CAD file, 2024-02-22]
Mechanical/Macrobot_Silvia Nur Aziza_Mechanical/db3.SLDPRT
4.00 x 80.0 x 60.0 mm
