hanzamzamy/arb-fpro/Mechanical/Macrobot_Silvia Nur Aziza_Mechanical/tg 3.SLDPRT

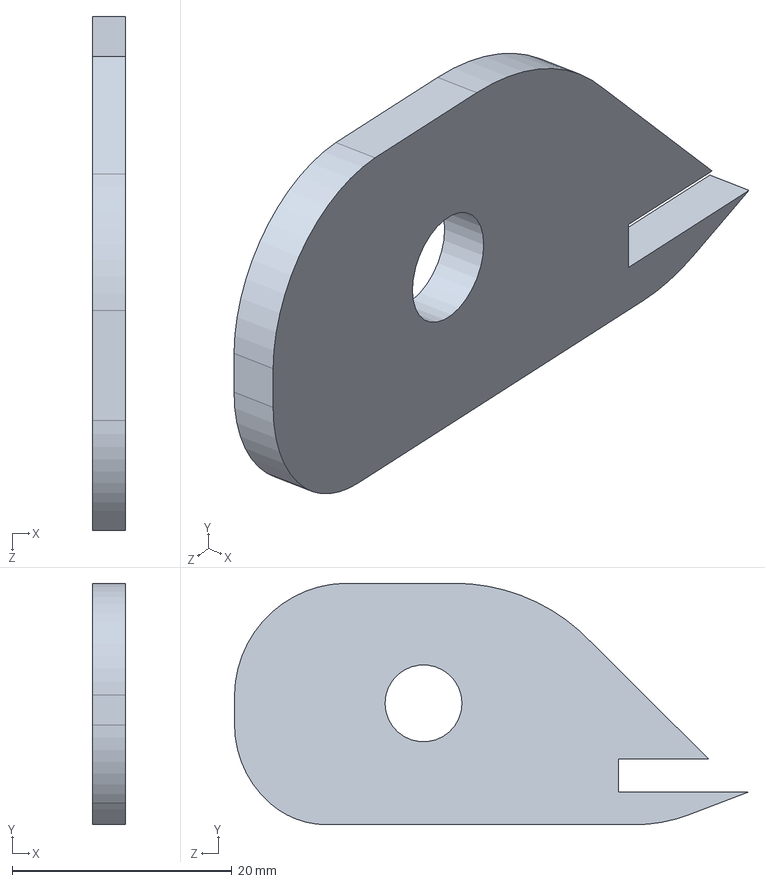
[picture p89: CAD file, 2024-02-22]
Mechanical/Macrobot_Silvia Nur Aziza_Mechanical/tg 3.SLDPRT
3.00 x 22.0 x 46.8 mm
