hanzamzamy/arb-fpro/Mechanical/Macrobot_Silvia Nur Aziza_Mechanical/db 4.SLDPRT

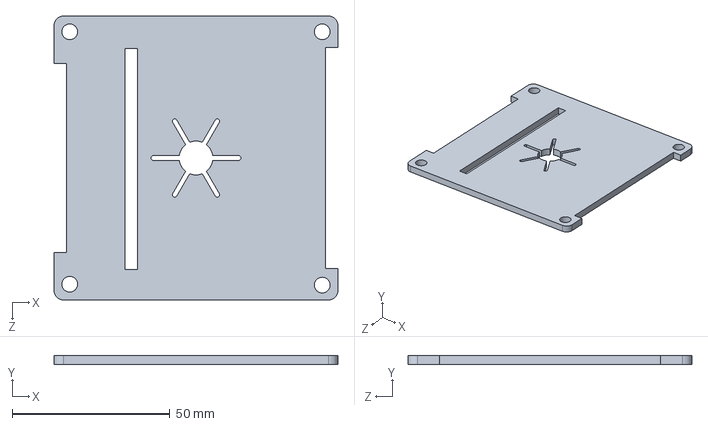
[picture p90: CAD file, 2024-02-22]
Mechanical/Macrobot_Silvia Nur Aziza_Mechanical/db 4.SLDPRT
90.0 x 3.00 x 90.0 mm
