hanzamzamy/arb-fpro/Mechanical/Macrobot_Silvia Nur Aziza_Mechanical/siliner.SLDPRT

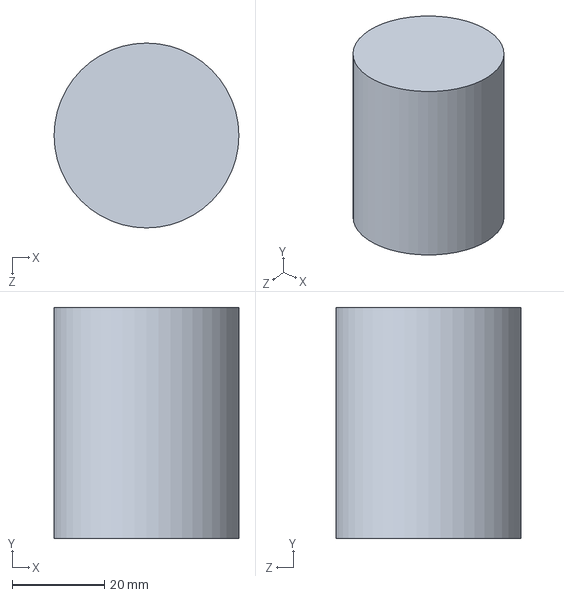
[picture p91: CAD file, 2024-02-22]
Mechanical/Macrobot_Silvia Nur Aziza_Mechanical/siliner.SLDPRT
40.0 x 50.0 x 40.0 mm
