hanzamzamy/arb-fpro/Mechanical/Macrobot_Silvia Nur Aziza_Mechanical/bs sisi selain yang berlubang (yg berlubang utuh.SLDPRT

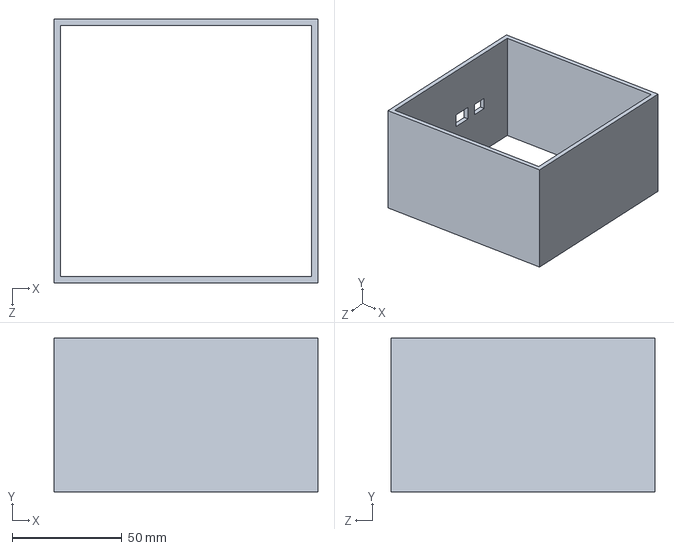
[picture p92: CAD file, 2024-02-22]
Mechanical/Macrobot_Silvia Nur Aziza_Mechanical/bs sisi selain yang berlubang (yg berlubang utuh.SLDPRT
120.0 x 70.0 x 120.0 mm
