hanzamzamy/arb-fpro/Mechanical/Macrobot_Silvia Nur Aziza_Mechanical/tg 1.SLDPRT

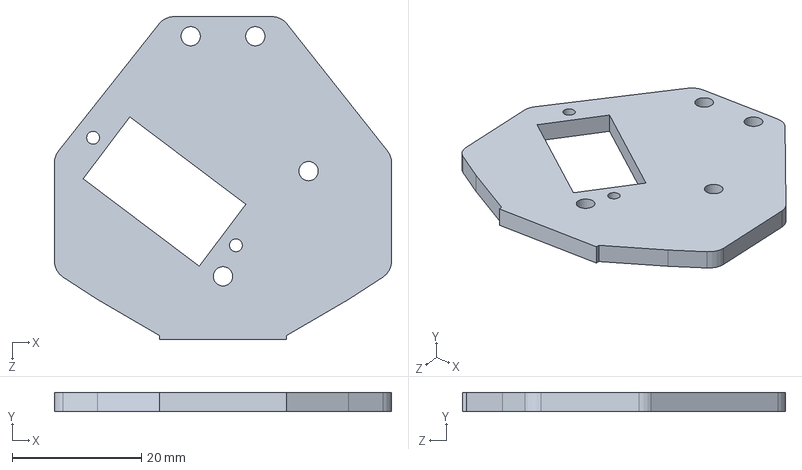
[picture p93: CAD file, 2024-02-22]
Mechanical/Macrobot_Silvia Nur Aziza_Mechanical/tg 1.SLDPRT
52.3 x 3.00 x 50.0 mm
